DiveNETGPS/Sealink-OEM/product/docs/images/img003.jpg

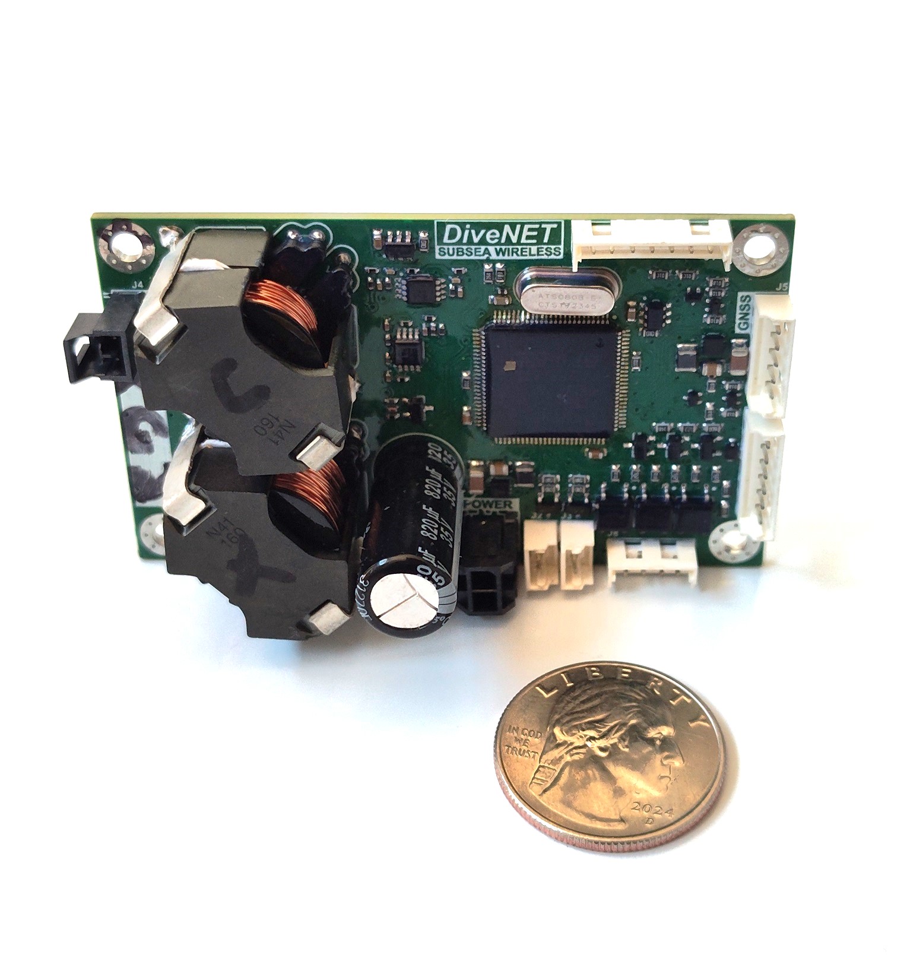
product/docs/images/img003.jpg
