DiveNETGPS/Sealink-OEM/product/docs/images/IMG_20260213_141653054.jpg

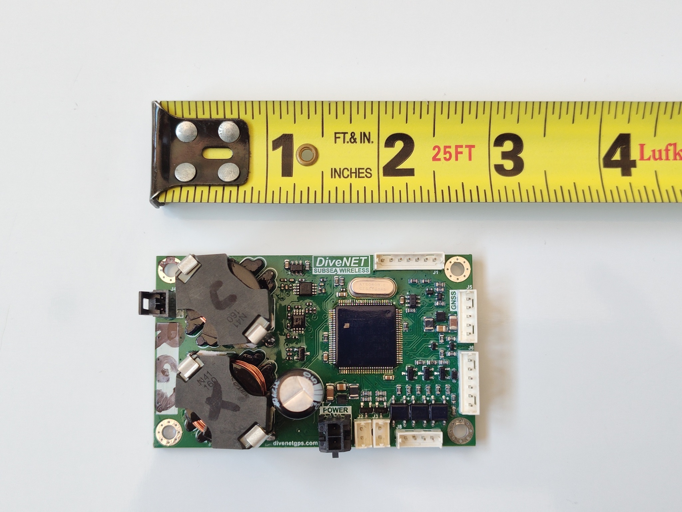
product/docs/images/IMG_20260213_141653054.jpg
