DiveNETGPS/Sealink-OEM/product/docs/images/IMG_20260213_142808760.jpg

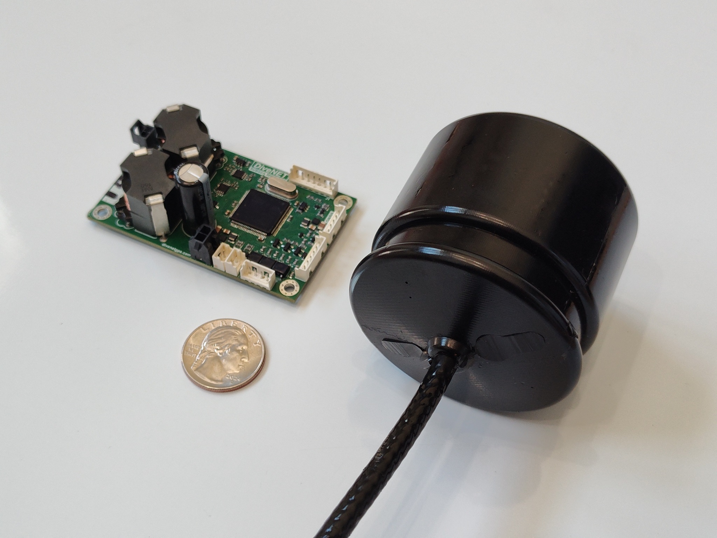
product/docs/images/IMG_20260213_142808760.jpg
